wlad1453/ChocoFactory/HW_PCB/MOSFETdrw.png

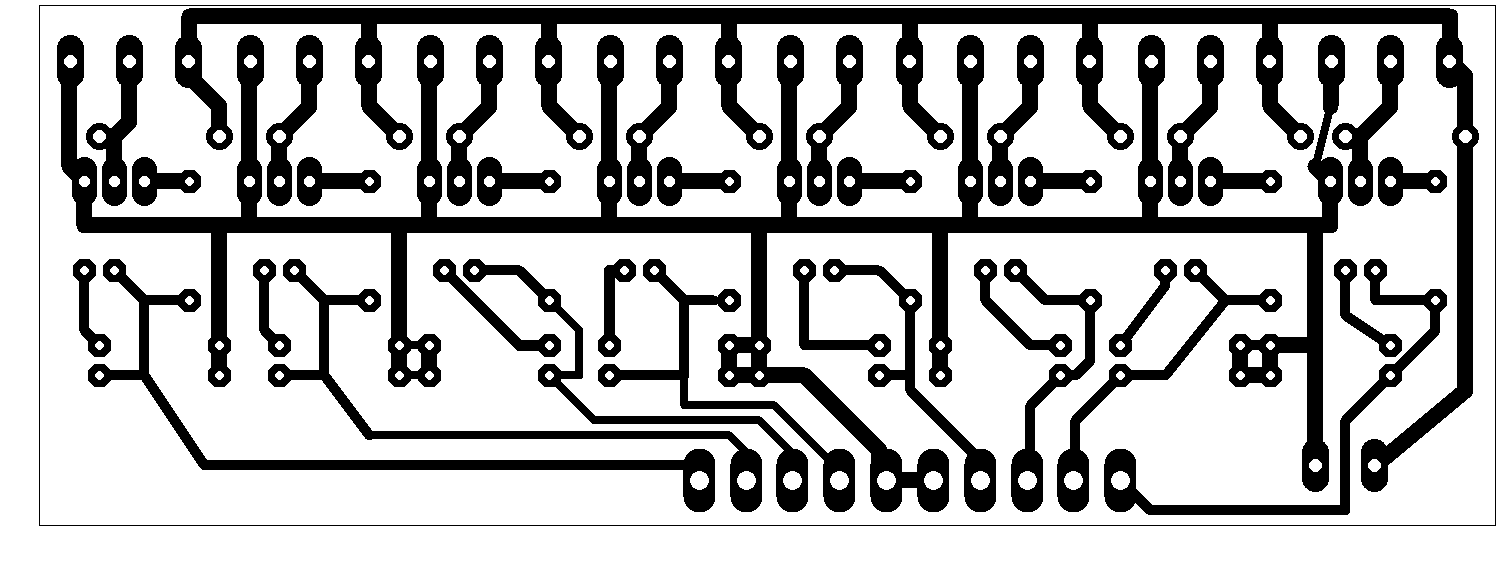
HW_PCB/MOSFETdrw.png
