wlad1453/ChocoFactory/Pictures/Pneumatic_island.jpg

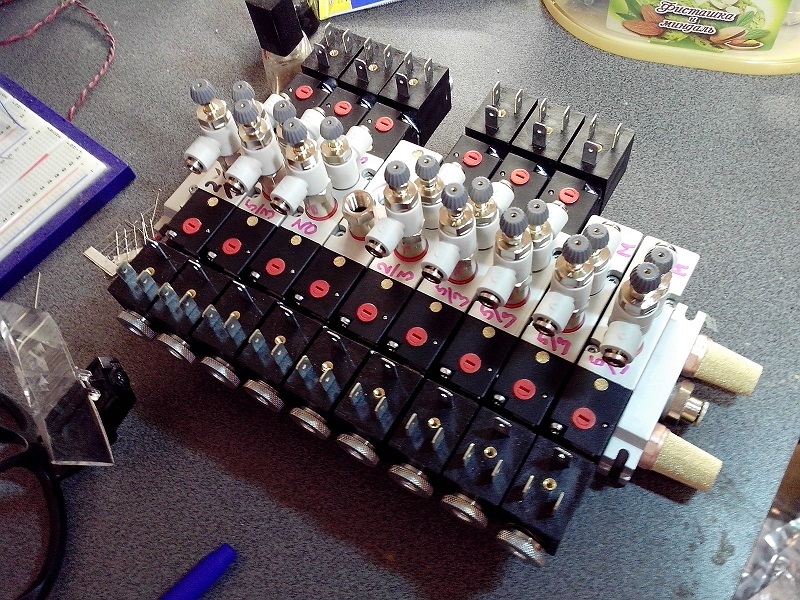
Pictures/Pneumatic_island.jpg
